gigijoe/modbus_gateway/main/pcf8574.hpp

/**
 * @brief PCF8574 arduino library
 * @author SkyWodd <skywodd@gmail.com>
 * @version 2.0
 * @link http://skyduino.wordpress.com/
 *
 * @section intro_sec Introduction
 * This class is designed to allow user to use PCF8574 gpio expander like any standard arduino pins.\n
 * This class provided standards arduino functions like pinMode, digitalWrite, digitalRead, ...\n
 * This new version is fully optimized and documented.\n
 * \n
 * Please report bug to <skywodd at gmail.com>
 *
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
 * @section other_sec Others notes and compatibility warning
 * Compatible with arduino 1.0.x and >=0023\n
 * Retro-compatible with the previous library version
 */
#ifndef _PCF8574_HPP
#define _PCF8574_HPP

#include <stdint.h>

#define INPUT             0x00
#define INPUT_PULLUP      0x02
#define OUTPUT            0x01
#define OUTPUT_PULLUP     0x03

/**
 * @brief PCF8574 Arduino class
 */
class PCF8574 {
public:
	/**
	 * Create a new PCF8574 instance
	 */
	PCF8574();

	uint8_t readRegister();

	void writeRegister(uint8_t regValue);

	/**
	 * Start the I2C controller and store the PCF8574 chip address
	 */
	void begin(uint8_t address = 0x21);

	/**
	 * Set the direction of a pin (OUTPUT, INPUT or INPUT_PULLUP)
	 * 
	 * @param pin The pin to set
	 * @param mode The new mode of the pin
	 * @remarks INPUT_PULLUP does physicaly the same thing as INPUT (no software pull-up resistors available) but is REQUIRED if you use external pull-up resistor
	 */
	void pinMode(uint8_t pin, uint8_t mode);
	void allPinsMode(uint8_t mode);

	/**
	 * Set the state of a pin (HIGH or LOW)
	 * 
	 * @param pin The pin to set
	 * @param value The new state of the pin
	 * @remarks Software pull-up resistors are not available on the PCF8574
	 */
	void digitalWrite(uint8_t pin, uint8_t value);

	/**
	 * Read the state of a pin
	 * 
	 * @param pin The pin to read back
	 * @return
	 */
	uint8_t digitalRead(uint8_t pin);

	/**
	 * Set the state of all pins in one go
	 * 
	 * @param value The new value of all pins (1 bit = 1 pin, '1' = HIGH, '0' = LOW)
	 */
	void write(uint8_t value);

	/**
	 * Read the state of all pins in one go
	 * 
	 * @return The current value of all pins (1 bit = 1 pin, '1' = HIGH, '0' = LOW)
	 */
	uint8_t read();

	/**
	 * Exactly like write(0x00), set all pins to LOW
	 */
	void clear();

	/**
	 * Exactly like write(0xFF), set all pins to HIGH
	 */
	void set();

	/**
	 * Toggle the state of a pin
	 */
	void toggle(uint8_t pin);

	/**
	 * Mark a pin as "pulled up"
	 * 
	 * @warning DO NOTHING - FOR RETRO COMPATIBILITY PURPOSE ONLY
	 * @deprecated
	 * @param pin Pin the mark as "pulled up"
	 */
	void pullUp(uint8_t pin);

	/**
	 * Mark a pin as "pulled down"
	 * 
	 * @warning DO NOTHING - FOR RETRO COMPATIBILITY PURPOSE ONLY
	 * @deprecated
	 * @param pin Pin the mark as "pulled down"
	 */
	void pullDown(uint8_t pin);

protected:
	/** Output pins values */
	volatile uint8_t _PORT;

	/** Current input pins values */
	volatile uint8_t _PIN;

	/** Pins modes values (OUTPUT or INPUT) */
	volatile uint8_t _DDR;

	/** PCF8574 I2C address */
	uint8_t _address;

	/** 
	 * Read GPIO states and store them in _PIN variable
	 *
	 * @remarks Before reading current GPIO states, current _PIN variable value is moved to _oldPIN variable
	 */
	void readGPIO();

	/** 
	 * Write value of _PORT variable to the GPIO
	 * 
	 * @remarks Only pin marked as OUTPUT are set, for INPUT pins their value are unchanged
	 * @warning To work properly (and avoid any states conflicts) readGPIO() MUST be called before call this function !
	 */
	void updateGPIO();
};

#endif
